tinkerlog/Kritzler/doc/img/m_img-3433.jpg

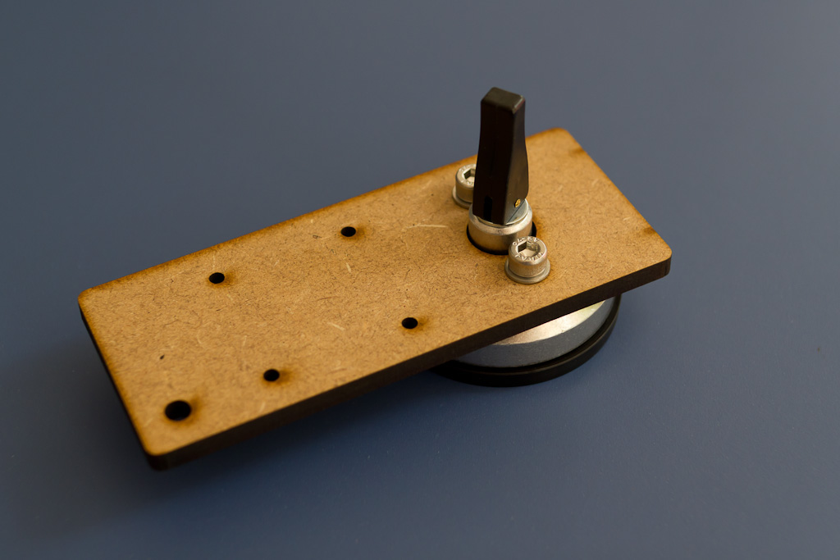
doc/img/m_img-3433.jpg
