tinkerlog/Kritzler/doc/img/m_img-3434.jpg

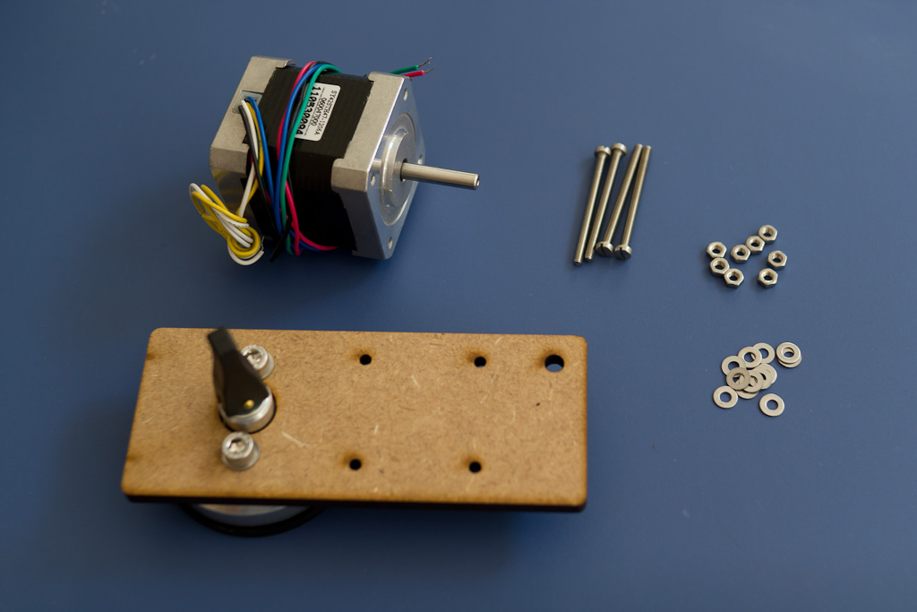
doc/img/m_img-3434.jpg
