tinkerlog/Kritzler/doc/img/m_img-3436.jpg

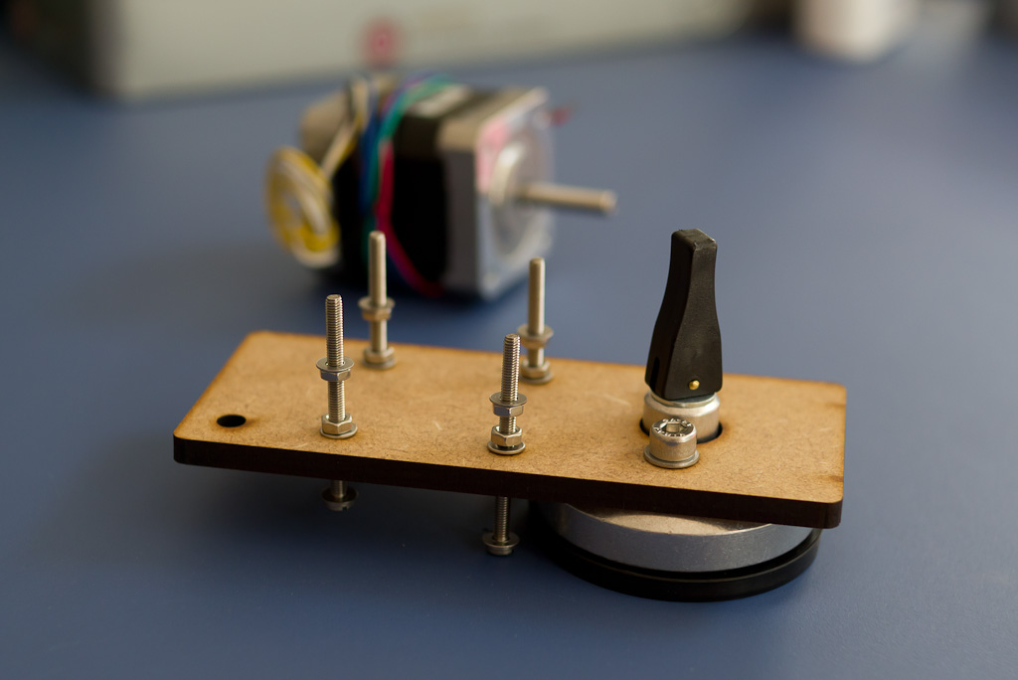
doc/img/m_img-3436.jpg
