tinkerlog/Kritzler/doc/img/m_img-3438.jpg

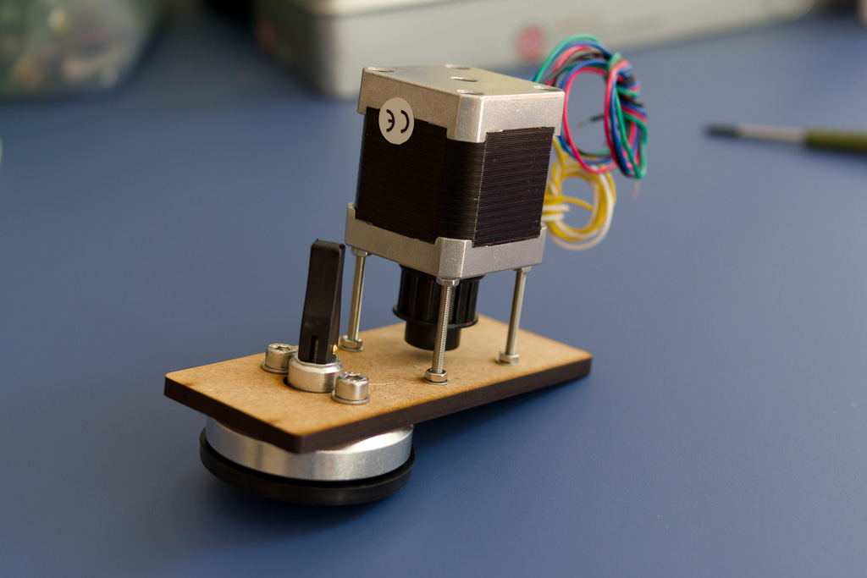
doc/img/m_img-3438.jpg
