tinkerlog/Kritzler/doc/img/m_img-3443.jpg

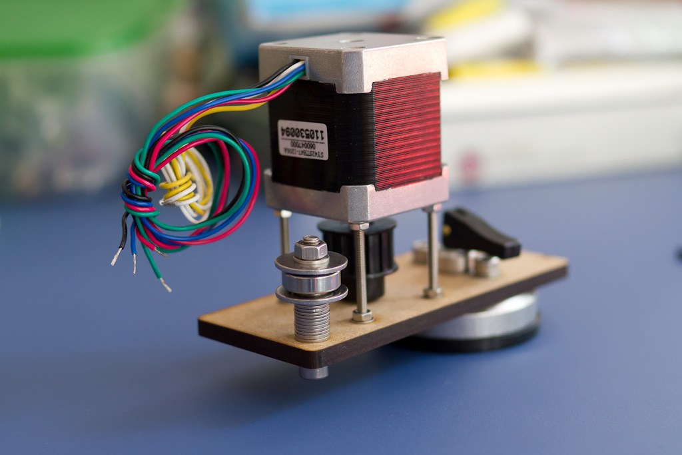
doc/img/m_img-3443.jpg
