tinkerlog/Kritzler/doc/img/m_img-3447.jpg

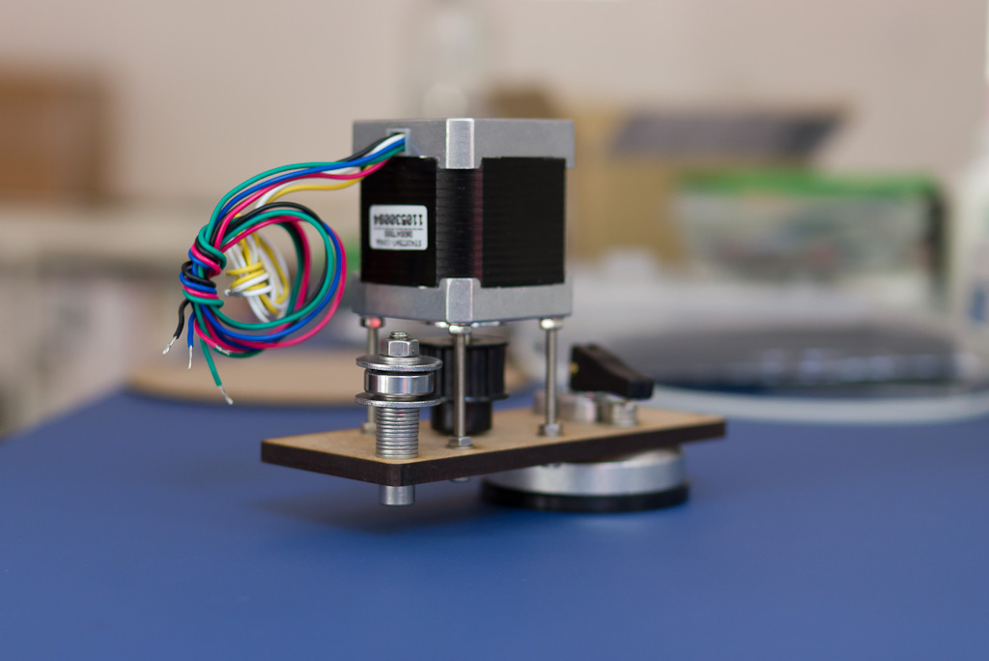
doc/img/m_img-3447.jpg
