tinkerlog/Kritzler/doc/img/m_img-3451.jpg

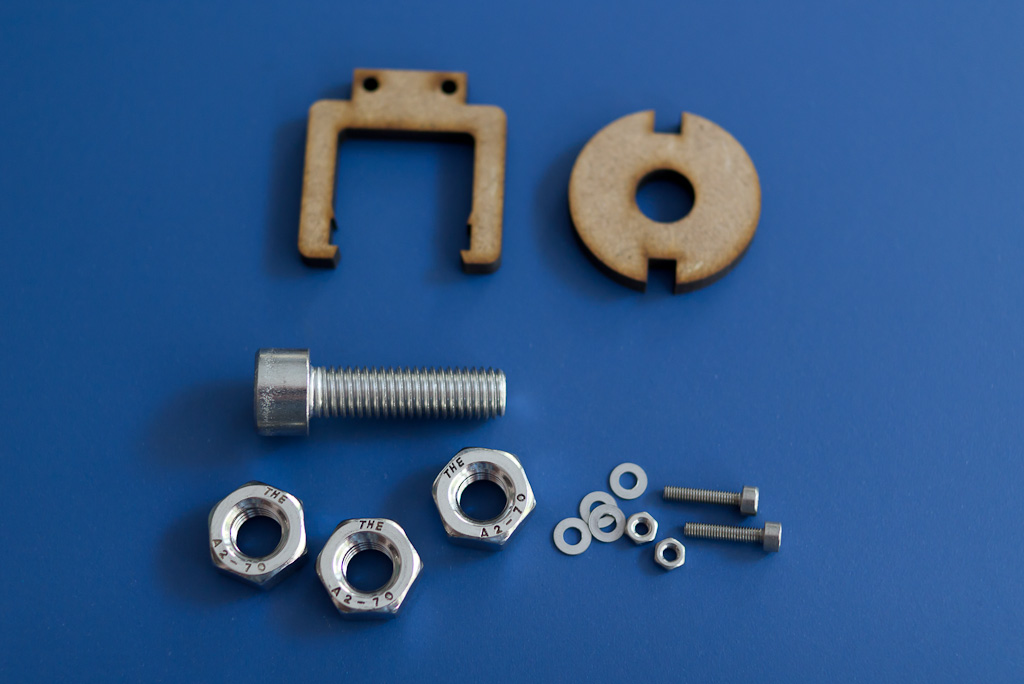
doc/img/m_img-3451.jpg
