tinkerlog/Kritzler/doc/img/m_img-3455.jpg

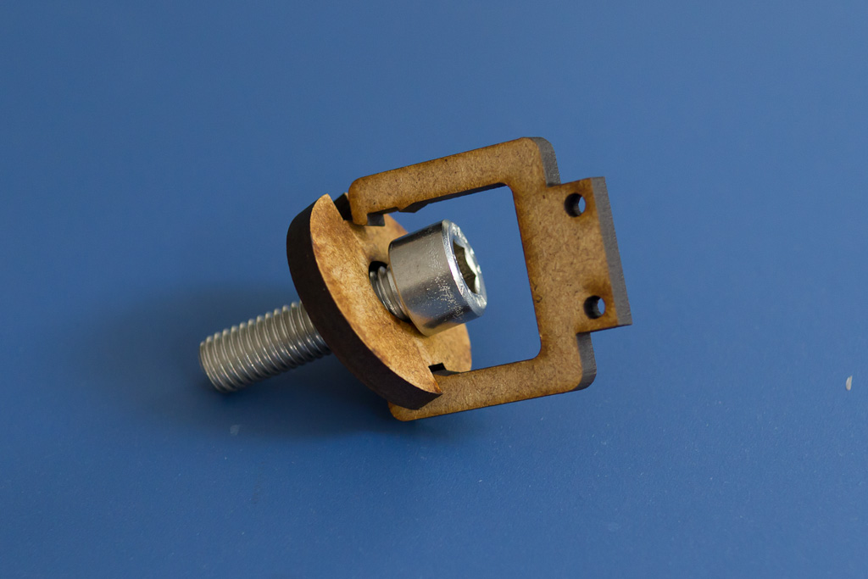
doc/img/m_img-3455.jpg
