tinkerlog/Kritzler/doc/img/m_img-3457.jpg

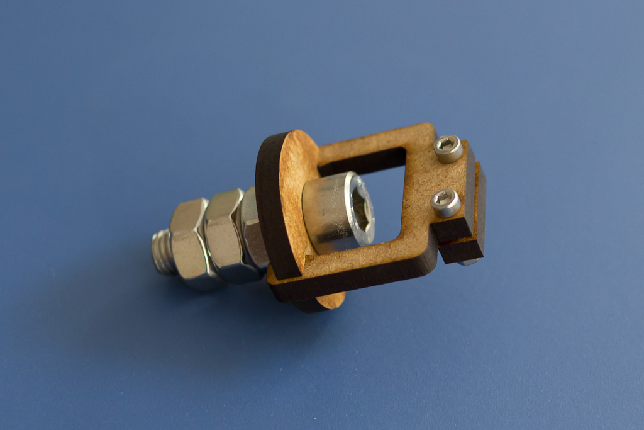
doc/img/m_img-3457.jpg
