tinkerlog/Kritzler/doc/img/m_img-3459.jpg

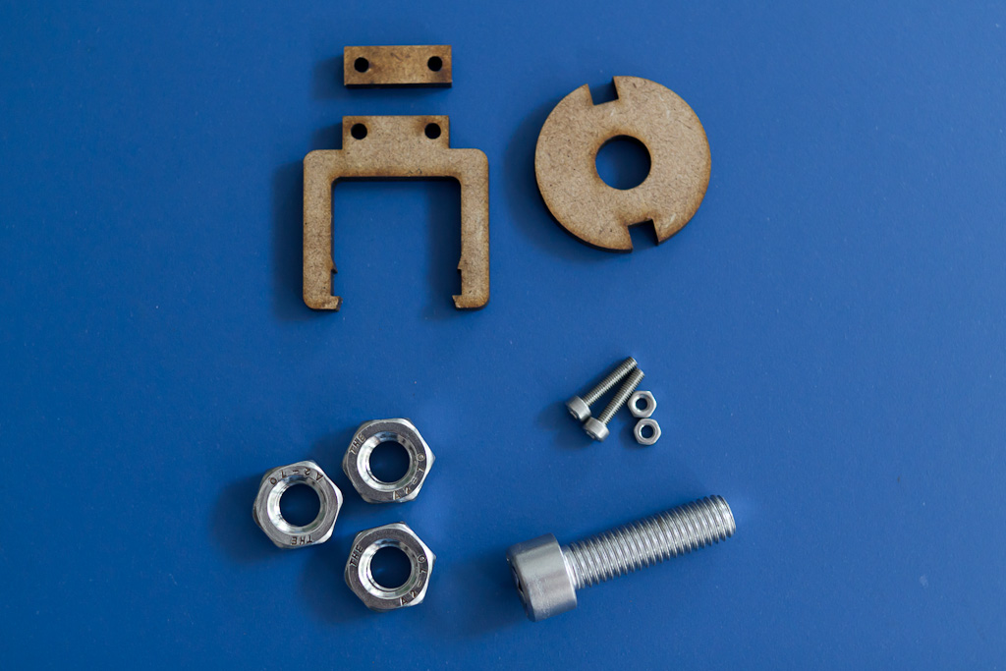
doc/img/m_img-3459.jpg
