tinkerlog/Kritzler/doc/img/m_img-3463.jpg

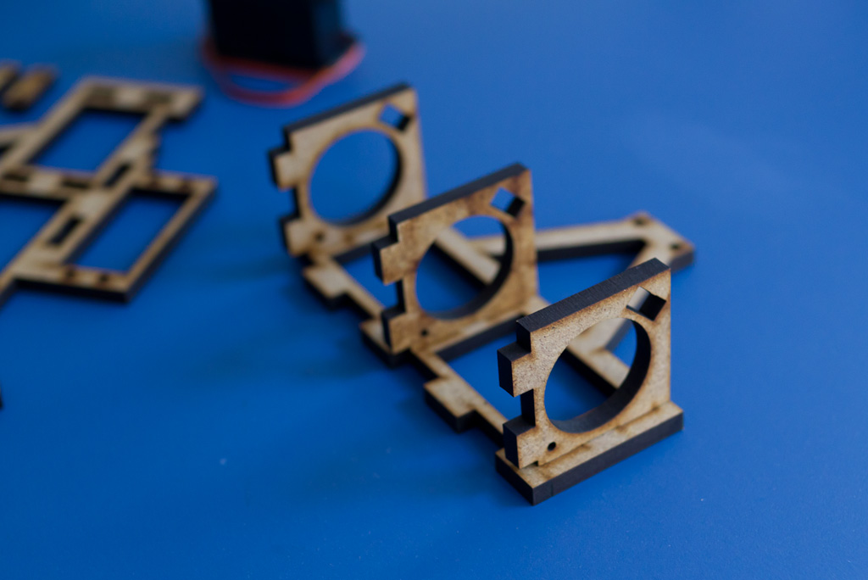
doc/img/m_img-3463.jpg
