tinkerlog/Kritzler/doc/img/m_img-3465.jpg

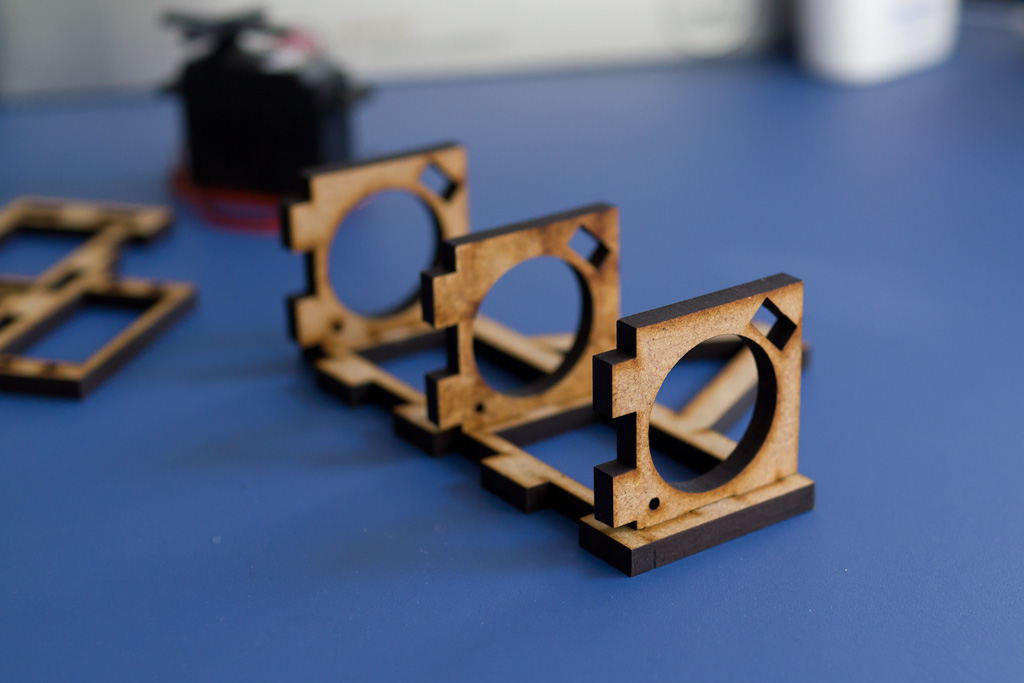
doc/img/m_img-3465.jpg
