tinkerlog/Kritzler/doc/img/m_img-3466.jpg

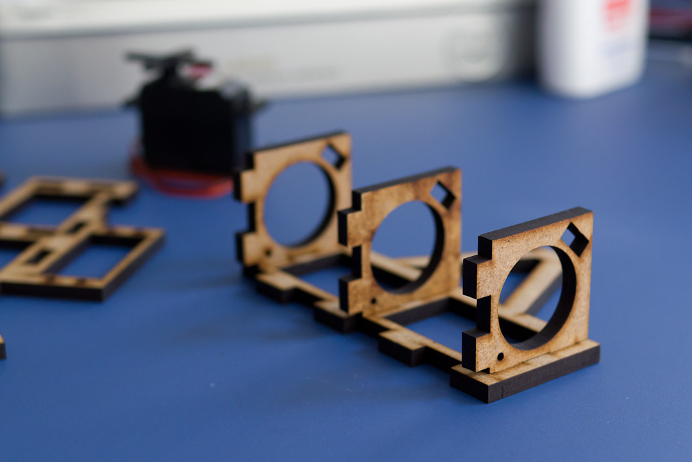
doc/img/m_img-3466.jpg
