tinkerlog/Kritzler/doc/img/m_img-3468.jpg

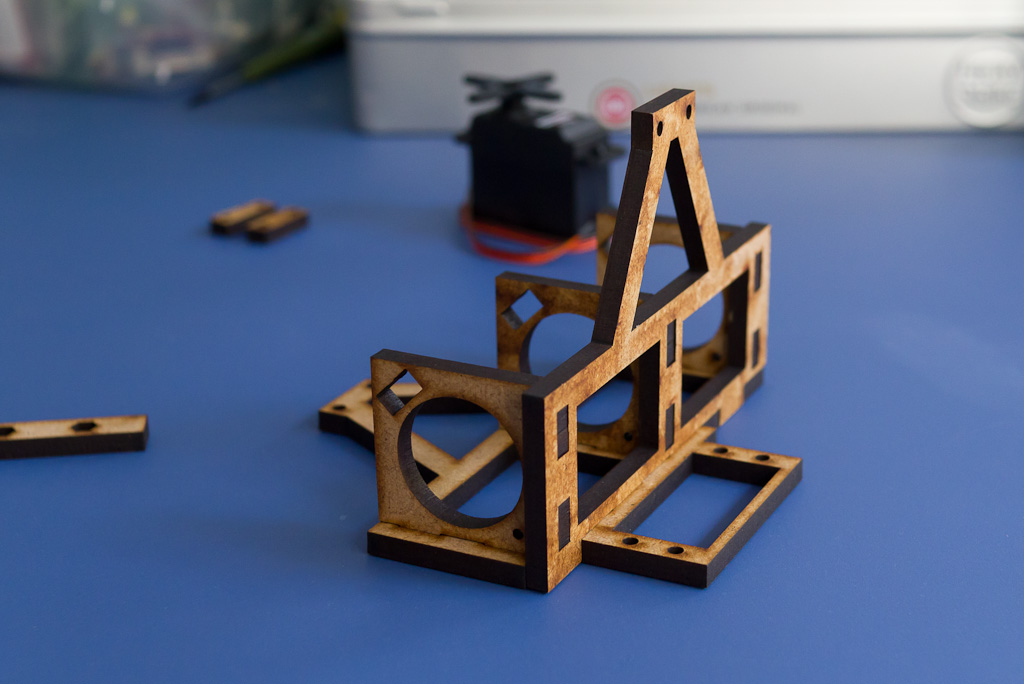
doc/img/m_img-3468.jpg
