tinkerlog/Kritzler/doc/img/m_img-3470.jpg

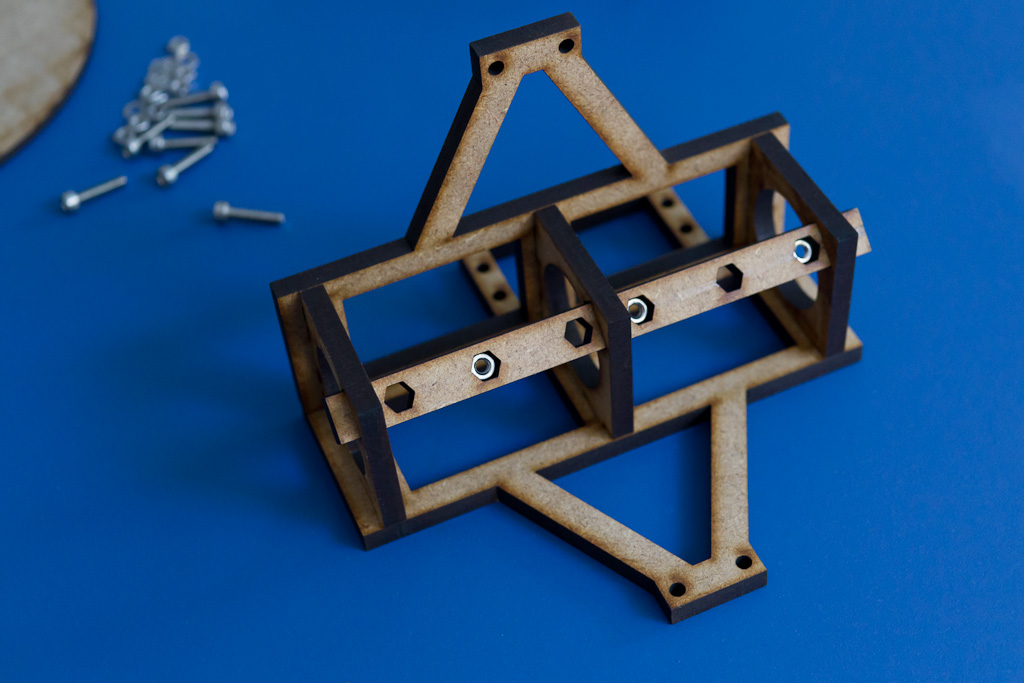
doc/img/m_img-3470.jpg
